JackSabine/BuckLinReg_5V/Draft1.asc

R1: res
R2: res
R3: res
R4: res
U1: LM108A
V1: voltage
V2: voltage
Named nets: 5, 0
