JackSabine/BuckLinReg_5V/ZenerSim.asc

D1: zener; PDZ3.0B
R1: res; {Rvar}
V1: voltage; 5
Named nets: 0, Vreg
.lib PDZ3_0B.prm
.step param Rvar list 1k 10k 100k
.tran 0 0.1m 0m 100n startup
